RandleH/Metope/doc/asset/rdme_config.jpg

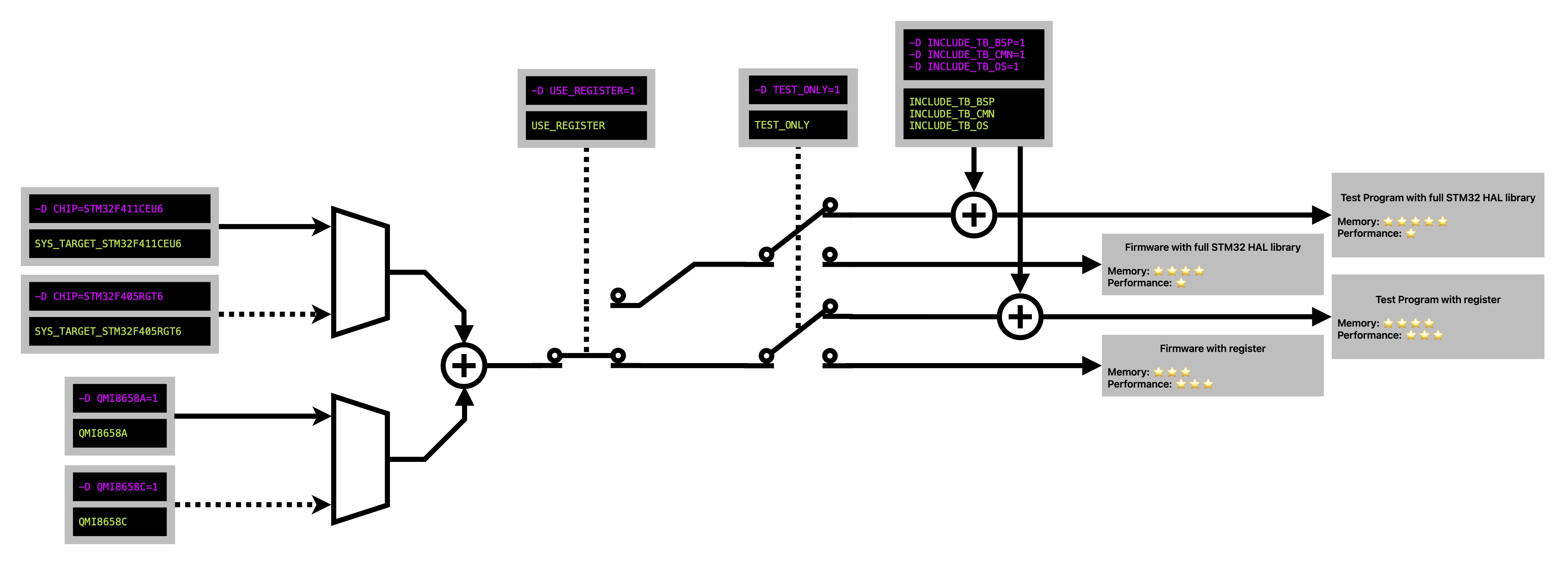
doc/asset/rdme_config.jpg
