RandleH/Metope/doc/asset/rdme_hierarchy.jpg

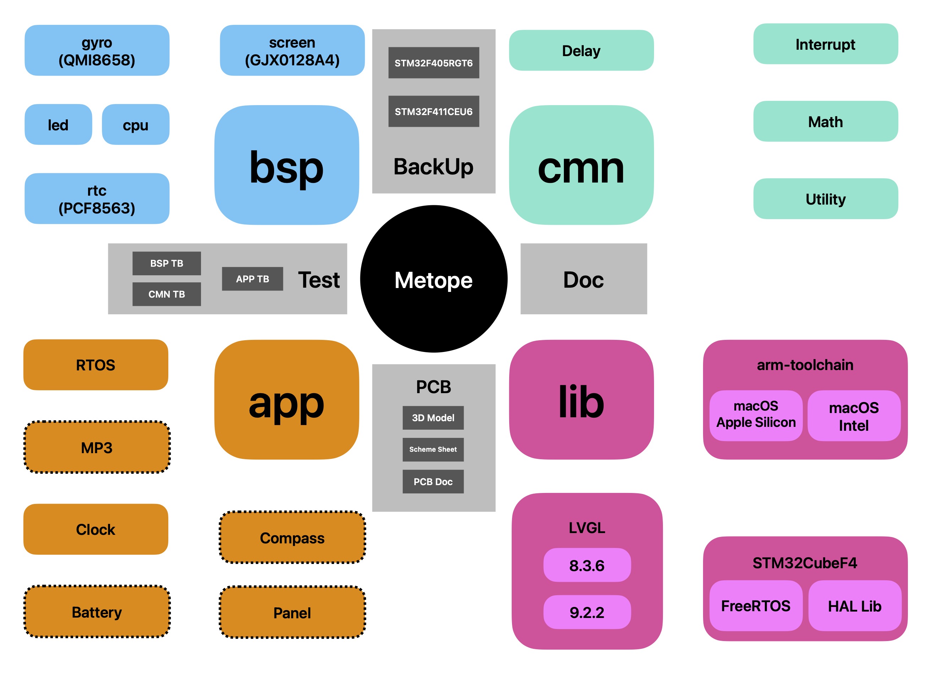
doc/asset/rdme_hierarchy.jpg
