RandleH/Metope/sqlstudio/assets/6.jpeg

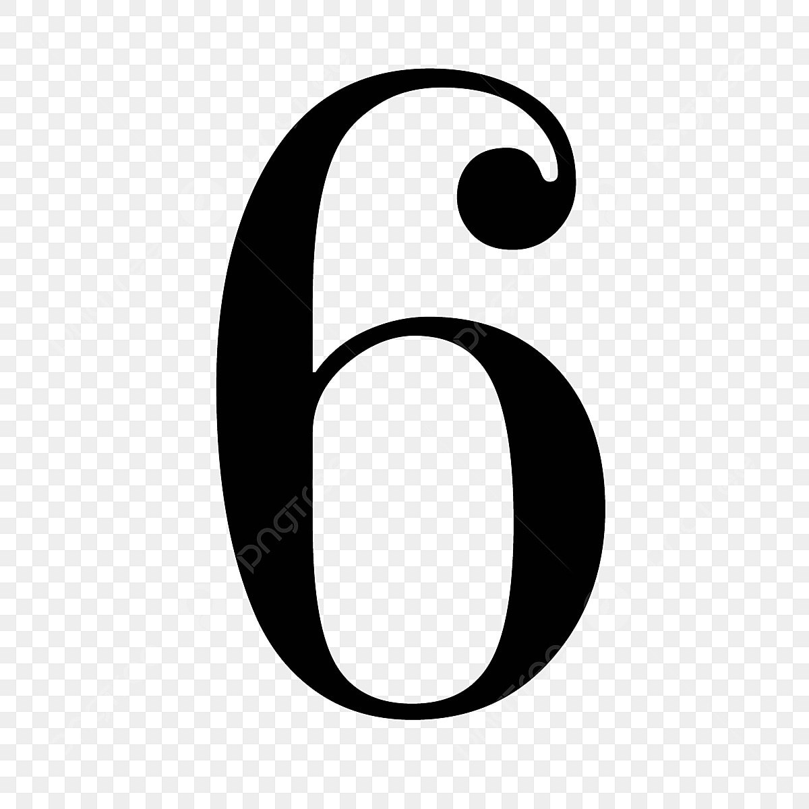
sqlstudio/assets/6.jpeg
