RandleH/Metope/sqlstudio/assets/6.png

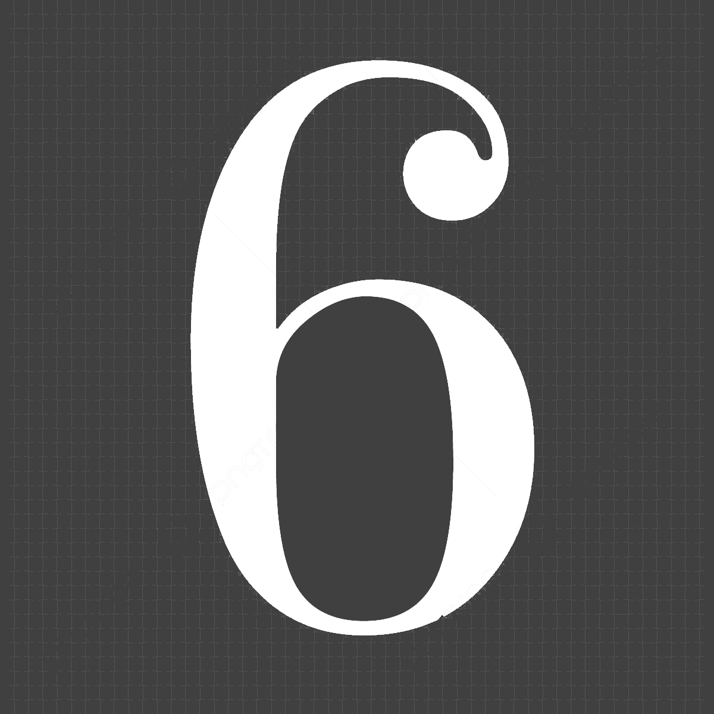
sqlstudio/assets/6.png
