RandleH/Metope/sqlstudio/assets/12.png

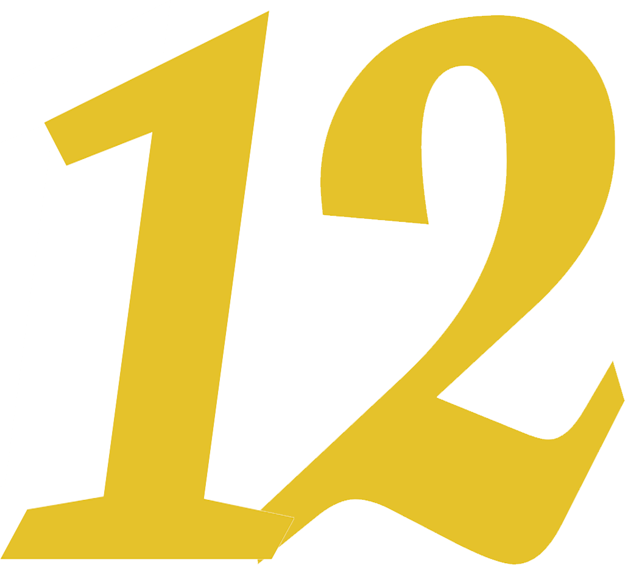
sqlstudio/assets/12.png
