RandleH/Metope/sqlstudio/assets/12handwritten.png

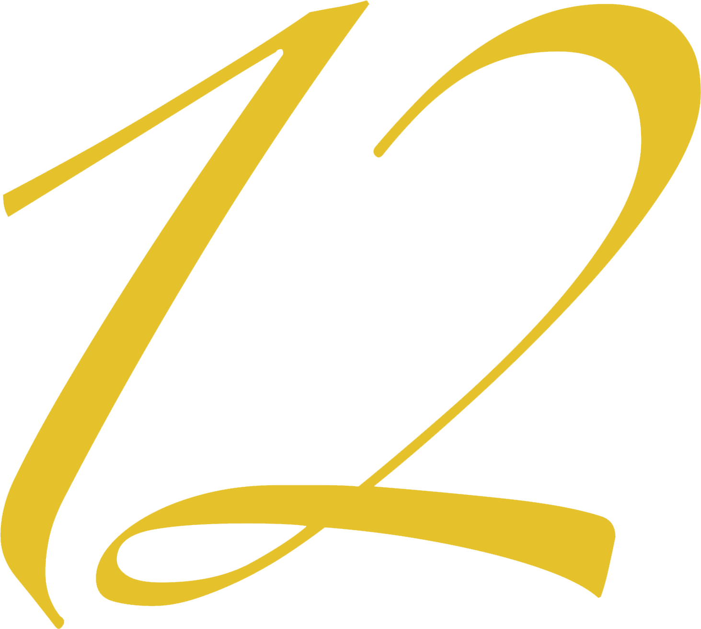
sqlstudio/assets/12handwritten.png
