RandleH/Metope/sqlstudio/assets/12roman.png

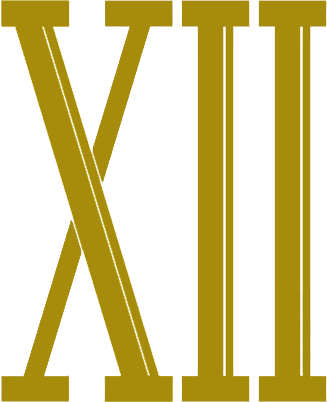
sqlstudio/assets/12roman.png
