RandleH/Metope/sqlstudio/assets/eyes_close.png

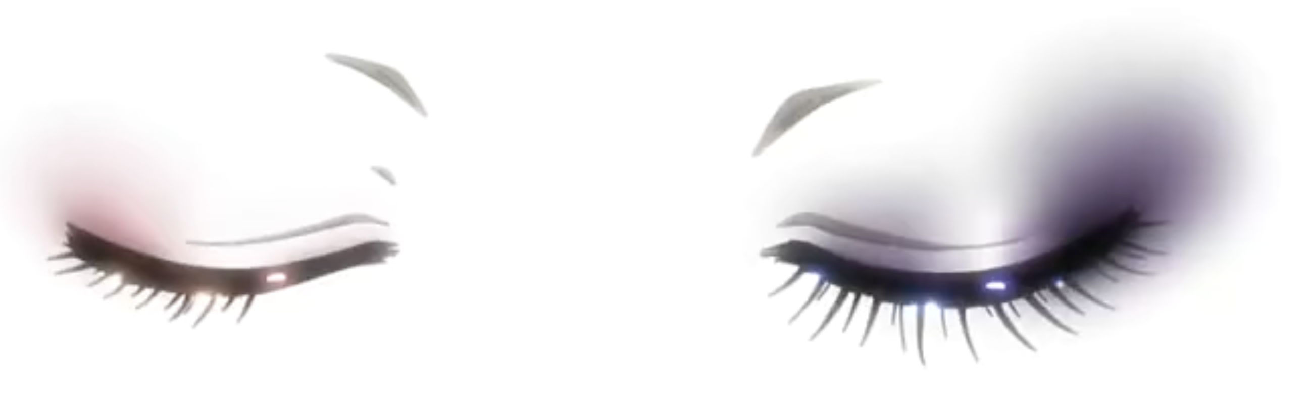
sqlstudio/assets/eyes_close.png
