RandleH/Metope/sqlstudio/assets/eyes_open.png

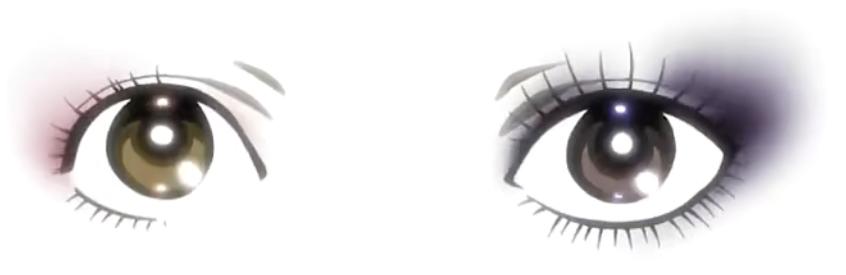
sqlstudio/assets/eyes_open.png
