RandleH/Metope/sqlstudio/assets/M.png

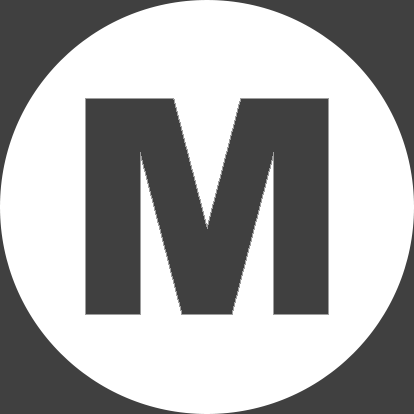
sqlstudio/assets/M.png
