RandleH/Metope/sqlstudio/assets/S.png

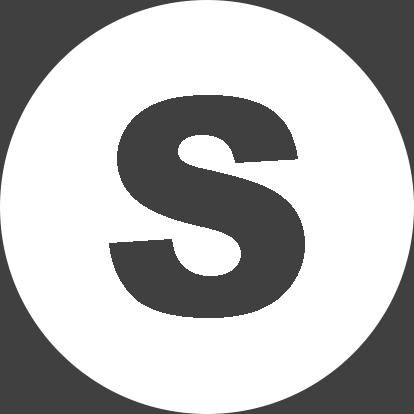
sqlstudio/assets/S.png
