RandleH/Metope/sqlstudio/assets/W.png

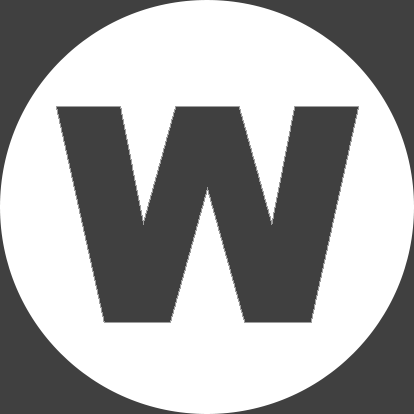
sqlstudio/assets/W.png
