RandleH/Metope/bsp/bsp_battery.c

/**
 ******************************************************************************
 * @file    bsp_battery.c
 * @author  RandleH
 * @brief   Board Support Package Delivery - Battery
 ******************************************************************************
 * @attention
 *
 * Copyright (c) 2025 RandleH.
 * All rights reserved.
 *
 * This software component is licensed by RandleH under BSD 3-Clause license,
 * the "License"; You may not use this file except in compliance with the
 * License. You may obtain a copy of the License at:
 *                        opensource.org/licenses/BSD-3-Clause
 *
 ******************************************************************************
*/

/* ************************************************************************** */
/*                                  Includes                                  */
/* ************************************************************************** */
#include "device.h"
#include "global.h"
#include "trace.h"
#include "bsp_battery.h"


/* ************************************************************************** */
/*                               Private Macros                               */
/* ************************************************************************** */
#define ADC_REPETITION_POW2   3
#define ADC_REPETITION        (1<<ADC_REPETITION_POW2)

#define MIN_BATTERY_ADC_VALUE 1850
#define MAX_BATTERY_ADC_VALUE 2450


/* ************************************************************************** */
/*                              Public Functions                              */
/* ************************************************************************** */
#ifdef __cplusplus
extern "C"{
#endif
/**
 * @note
 *  Analog Battery Voltage Range: 1800mv ~ 2150mv => 1450 ~ 1732 (This value is subject to the actual measurement)
 *  Periphral ADC Range Mapping: 0mv ~ 3300mv => 0 ~ 4095 (12Bit)
 *  Function Output Range: 0 ~ 255 (8Bit)
 */
uint8_t bsp_battery_measure(void){
  uint32_t raw = 0;
  {
    HAL_ADC_Start(metope.bsp.pHadc1);

  /**
   * @todo
   *  `HAL_ADC_PollForConversion()` is getting stuck.
   */
#if 0
    for(int i=0; i<ADC_REPETITION; ++i){
      HAL_ADC_PollForConversion(metope.bsp.pHadc1, HAL_MAX_DELAY);
      raw += HAL_ADC_GetValue(metope.bsp.pHadc1);
    }
    raw >>= ADC_REPETITION_POW2;
#else
    HAL_ADC_PollForConversion(metope.bsp.pHadc1, HAL_MAX_DELAY);
    raw = HAL_ADC_GetValue(metope.bsp.pHadc1);
#endif

    HAL_ADC_Stop(metope.bsp.pHadc1);
  }

  uint32_t raw_copy = raw;

  if( raw_copy > MAX_BATTERY_ADC_VALUE ){
    raw_copy = MAX_BATTERY_ADC_VALUE;
  }else if( raw_copy < MIN_BATTERY_ADC_VALUE ){
    raw_copy = MIN_BATTERY_ADC_VALUE;
  }

  uint8_t ans = (uint8_t)(((raw_copy - MIN_BATTERY_ADC_VALUE)<<8) / (MAX_BATTERY_ADC_VALUE-MIN_BATTERY_ADC_VALUE+1));

  TRACE_DUMMY("BSP - Battery ADC raw=%u raw_copy=%u ans=%u", raw, raw_copy, ans);
  return ans;
}


#ifdef __cplusplus
}
#endif



  // DEBUG: BSP - Battery ADC raw=2600 raw_copy=2450 ans=255
  // DEBUG: BSP - Battery ADC raw=2460 raw_copy=2450 ans=255
  // DEBUG: BSP - Battery ADC raw=2382 raw_copy=2382 ans=226
  // DEBUG: BSP - Battery ADC raw=2319 raw_copy=2319 ans=199
  // DEBUG: CMN - Time increased to 2025/1/21 1:40:0
  // DEBUG: BSP - Battery ADC raw=2403 raw_copy=2403 ans=235
  // DEBUG: BSP - Battery ADC raw=2336 raw_copy=2336 ans=207
  // DEBUG: BSP - Battery ADC raw=2241 raw_copy=2241 ans=166
  // DEBUG: BSP - Battery ADC raw=2327 raw_copy=2327 ans=203
  // DEBUG: BSP - Battery ADC raw=2310 raw_copy=2310 ans=195
  // DEBUG: BSP - Battery ADC raw=2279 raw_copy=2279 ans=182
  // DEBUG: BSP - Battery ADC raw=2286 raw_copy=2286 ans=185
  // DEBUG: BSP - Battery ADC raw=2328 raw_copy=2328 ans=203
  // DEBUG: BSP - Battery ADC raw=2287 raw_copy=2287 ans=186
  // DEBUG: BSP - Battery ADC raw=2266 raw_copy=2266 ans=177
  // DEBUG: BSP - Battery ADC raw=2318 raw_copy=2318 ans=199
  // DEBUG: BSP - Battery ADC raw=2282 raw_copy=2282 ans=184
  // DEBUG: BSP - Battery ADC raw=2284 raw_copy=2284 ans=184
  // DEBUG: BSP - Battery ADC raw=2336 raw_copy=2336 ans=207
  // DEBUG: BSP - Battery ADC raw=2262 raw_copy=2262 ans=175
  // DEBUG: BSP - Battery ADC raw=2278 raw_copy=2278 ans=182
  // DEBUG: BSP - Battery ADC raw=2260 raw_copy=2260 ans=174
  // DEBUG: BSP - Battery ADC raw=2271 raw_copy=2271 ans=179
  // DEBUG: BSP - Battery ADC raw=2310 raw_copy=2310 ans=195
  // DEBUG: BSP - Battery ADC raw=2334 raw_copy=2334 ans=206
  // DEBUG: CMN - Time increased to 2025/1/21 1:41:0
  // DEBUG: BSP - Battery ADC raw=2255 raw_copy=2255 ans=172
  // DEBUG: BSP - Battery ADC raw=2299 raw_copy=2299 ans=191
  // DEBUG: BSP - Battery ADC raw=2254 raw_copy=2254 ans=172
  // DEBUG: BSP - Battery ADC raw=2266 raw_copy=2266 ans=177
  // DEBUG: BSP - Battery ADC raw=2260 raw_copy=2260 ans=174
  // DEBUG: BSP - Battery ADC raw=2270 raw_copy=2270 ans=178
  // DEBUG: BSP - Battery ADC raw=2260 raw_copy=2260 ans=174
  // DEBUG: BSP - Battery ADC raw=2347 raw_copy=2347 ans=211
  // DEBUG: BSP - Battery ADC raw=2220 raw_copy=2220 ans=157
  // DEBUG: BSP - Battery ADC raw=2296 raw_copy=2296 ans=189
  // DEBUG: BSP - Battery ADC raw=2254 raw_copy=2254 ans=172
  // DEBUG: BSP - Battery ADC raw=2234 raw_copy=2234 ans=163
  // DEBUG: BSP - Battery ADC raw=2196 raw_copy=2196 ans=147
  // DEBUG: BSP - Battery ADC raw=2251 raw_copy=2251 ans=170
  // DEBUG: BSP - Battery ADC raw=2248 raw_copy=2248 ans=169
  // DEBUG: BSP - Battery ADC raw=2334 raw_copy=2334 ans=206
  // DEBUG: BSP - Battery ADC raw=2294 raw_copy=2294 ans=189
  // DEBUG: BSP - Battery ADC raw=2244 raw_copy=2244 ans=167
  // DEBUG: BSP - Battery ADC raw=2271 raw_copy=2271 ans=179
  // DEBUG: BSP - Battery ADC raw=2296 raw_copy=2296 ans=189
  // DEBUG: CMN - Time increased to 2025/1/21 1:42:0
  // DEBUG: BSP - Battery ADC raw=2366 raw_copy=2366 ans=219
  // DEBUG: BSP - Battery ADC raw=2135 raw_copy=2135 ans=121
  // DEBUG: BSP - Battery ADC raw=2231 raw_copy=2231 ans=162
  // DEBUG: BSP - Battery ADC raw=2094 raw_copy=2094 ans=103
  // DEBUG: BSP - Battery ADC raw=2295 raw_copy=2295 ans=189
  // DEBUG: BSP - Battery ADC raw=2222 raw_copy=2222 ans=158
  // DEBUG: BSP - Battery ADC raw=2286 raw_copy=2286 ans=185
  // DEBUG: BSP - Battery ADC raw=2245 raw_copy=2245 ans=168
  // DEBUG: BSP - Battery ADC raw=2226 raw_copy=2226 ans=160
  // DEBUG: BSP - Battery ADC raw=2242 raw_copy=2242 ans=166
  // DEBUG: BSP - Battery ADC raw=2239 raw_copy=2239 ans=165
  // DEBUG: BSP - Battery ADC raw=2252 raw_copy=2252 ans=171
  // DEBUG: BSP - Battery ADC raw=2226 raw_copy=2226 ans=160
  // DEBUG: BSP - Battery ADC raw=2210 raw_copy=2210 ans=153
  // DEBUG: BSP - Battery ADC raw=2234 raw_copy=2234 ans=163
  // DEBUG: BSP - Battery ADC raw=2239 raw_copy=2239 ans=165
  // DEBUG: BSP - Battery ADC raw=2218 raw_copy=2218 ans=156
  // DEBUG: BSP - Battery ADC raw=2277 raw_copy=2277 ans=181
  // DEBUG: BSP - Battery ADC raw=2234 raw_copy=2234 ans=163
  // DEBUG: BSP - Battery ADC raw=2287 raw_copy=2287 ans=186
  // DEBUG: CMN - Time increased to 2025/1/21 1:43:0
  // DEBUG: BSP - Battery ADC raw=2230 raw_copy=2230 ans=161
  // DEBUG: BSP - Battery ADC raw=2230 raw_copy=2230 ans=161
  // DEBUG: BSP - Battery ADC raw=2240 raw_copy=2240 ans=166
  // DEBUG: BSP - Battery ADC raw=2190 raw_copy=2190 ans=144
  // DEBUG: BSP - Battery ADC raw=2266 raw_copy=2266 ans=177
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
  // DEBUG: BSP - Battery ADC raw=2614 raw_copy=2450 ans=255
  // DEBUG: BSP - Battery ADC raw=2558 raw_copy=2450 ans=255
  // DEBUG: BSP - Battery ADC raw=2542 raw_copy=2450 ans=255


/* ********************************** EOF *********************************** */
