RandleH/Metope/bsp/bsp_timer.c

/**
 ******************************************************************************
 * @file    bsp_timer.c
 * @author  RandleH
 * @brief   Board Support Package Delivery - Timer
 ******************************************************************************
 * @attention
 *
 * Copyright (c) 2022 RandleH.
 * All rights reserved.
 *
 * This software component is licensed by RandleH under BSD 3-Clause license,
 * the "License"; You may not use this file except in compliance with the
 * License. You may obtain a copy of the License at:
 *                        opensource.org/licenses/BSD-3-Clause
 *
 ******************************************************************************
*/


/* ************************************************************************** */
/*                                  Includes                                  */
/* ************************************************************************** */
#include "global.h"
#include "device.h"
#include "assert.h"
#include "bsp_timer.h"


/* ************************************************************************** */
/*                             Private Functions                              */
/* ************************************************************************** */
#ifdef __cplusplus
extern "C"{
#endif

/**
 * @brief Timer Register Initialization
 * @param [in] TIMx      - Timer Base Address
 * @param [in] Prescaler - Timer Prescaler
 * @addtogroup MachineDependent
 */
static void bsp_timer_init_register( TIM_TypeDef *TIMx, uint32_t psc){
  TIMx->ARR = 10U;
  TIMx->PSC = psc;

  SET_BIT( TIMx->EGR, TIM_EGR_UG );   // Generate an update
  SET_BIT( TIMx->CR1, TIM_CR1_DIR);   // Down Counter
  SET_BIT( TIMx->CR1, TIM_CR1_URS);   // Update only when overflow
  SET_BIT( TIMx->CR1, TIM_CR1_OPM);   // One-pulse mode
  CLEAR_BIT( TIMx->CR1, TIM_CR1_CMS_0);
  CLEAR_BIT( TIMx->CR1, TIM_CR1_CMS_1);
  CLEAR_BIT( TIMx->CR1, TIM_CR1_ARPE);  // Auto-reload preload
  CLEAR_BIT( TIMx->CR1, TIM_CR1_CKD_0); // No clock division
  CLEAR_BIT( TIMx->CR1, TIM_CR1_CKD_1);
  TIMx->SR = 0x00000000;
  SET_BIT( TIMx->DIER, TIM_DIER_UIE);
  SET_BIT( TIMx->CR1, TIM_CR1_CEN);  // Enable timer

  u16 cnt  = 0xFFFF;
  switch((u32)(TIMx)){
    case TIM2_BASE:{
      while( metope.bsp.status->tim2[0]==0 && --cnt!=0);
      metope.bsp.status->tim2[0] = 0;
      break;
    }
    case TIM9_BASE:{
      while( metope.bsp.status->tim9[0]==0 && --cnt!=0);
      metope.bsp.status->tim9[0] = 0;
      extern uint32_t TIM9_FLAG;
      TIM9_FLAG = 0;
      break;
    }
    default:{
      ASSERT( 0, "Unknown timer base");
      break;
    }
  }

  CLEAR_BIT( TIMx->CR1, TIM_CR1_CEN);  // Disable timer
}

#ifdef __cplusplus
}
#endif


/* ************************************************************************** */
/*                              Public Functions                              */
/* ************************************************************************** */
#ifdef __cplusplus
extern "C"{
#endif
/**
 * @brief Timer Initialization
 * @addtogroup MachineDependent
 */
void bsp_timer_init( void){
  
  __HAL_RCC_TIM2_CLK_ENABLE();
  __HAL_RCC_TIM9_CLK_ENABLE();
  
  HAL_NVIC_SetPriority(TIM2_IRQn, 0, 0);
  HAL_NVIC_SetPriority(TIM1_BRK_TIM9_IRQn, 0, 0);
  HAL_NVIC_EnableIRQ(TIM2_IRQn);
  HAL_NVIC_EnableIRQ(TIM1_BRK_TIM9_IRQn);

  /**
   * @note: 
   *  f_TIMx = f_APB/( ${psc}+1 )
   *  MaxDelay = [(1<<NUM_CNT_BITS)-1] / f_TIMx
   */
#if (defined SYS_TARGET_STM32F411CEU6) || (defined EMULATOR_STM32F411CEU6)
  bsp_timer_init_register( TIM2, 46875-1); /*!< APB1 = 96MHz; f_TIM2 = 2.048kHz; CNT[0:15]; MaxDelay = 32000ms  */
  bsp_timer_init_register( TIM9, 96-1);    /*!< APB1 = 96MHz; f_TIM9 = 1MHz;     CNT[0:15]; MaxDelay = 65.536ms */
#elif (defined SYS_TARGET_STM32F405RGT6) || (defined EMULATOR_STM32F405RGT6)
  bsp_timer_init_register( TIM2, 23437-1); /*!< APB1 = 48MHz; f_TIM2 = 2.048kHz; CNT[0:15]; MaxDelay = 32000ms  */
  bsp_timer_init_register( TIM9, 48-1);    /*!< APB1 = 48MHz; f_TIM9 = 1MHz;     CNT[0:15]; MaxDelay = 65.536ms */
#else
  #error "Unimplemented"
#endif

}


/**
 * @brief Enable the Timer(TIM2) Counting
 * @note Timer frequency: f_TIM2 = 2.048kHz
 * @param [in] ms - Milliseconds | MaxDelay = 32000ms
 * @addtogroup MachineDependent
 */
void bsp_tim2_delay(u16 ms){
  TIM2->ARR = ms * 2048 / 1000;
  CLEAR_BIT( TIM2->SR, TIM_SR_UIF);
  SET_BIT( TIM2->EGR, TIM_EGR_UG);
  SET_BIT( TIM2->CR1, TIM_CR1_CEN);
}


/**
 * @brief Enable the Timer(TIM9) Counting
 * @note Timer frequency: f_TIM9 = 1MHz
 * @param [in] us - Microseconds | MaxDelay = 65535us
 * @addtogroup MachineDependent
 */
void bsp_tim9_delay(u16 us){
  TIM9->ARR = us;
  CLEAR_BIT( TIM9->SR, TIM_SR_UIF);
  SET_BIT( TIM9->EGR, TIM_EGR_UG);
  SET_BIT( TIM9->CR1, TIM_CR1_CEN);
}

#ifdef __cplusplus
}
#endif

/* ********************************** EOF *********************************** */
