RandleH/Metope/top/init.h

#ifndef __INIT_H__
#define __INIT_H__


#ifdef __cplusplus
extern "C"{
#endif

void hw_init(void);
void data_init(void);
void bsp_init(void);
void app_init(void);
void os_init(void);

#ifdef __cplusplus
}
#endif

#endif
